m9aertner/ATtiny-PinKeepAlive/Arduino.h

/*
 * Arduino.h - Just some typedefs to make the TinySMLDecoderTest compile standalone ... 
 */
typedef unsigned char byte;
typedef unsigned char uint8_t;
typedef signed char int8_t;
typedef short unsigned int uint16_t;
typedef short signed int int16_t;
typedef signed long int32_t;
typedef unsigned long uint32_t;
typedef signed long long int64_t;
typedef unsigned long long uint64_t;
