m9aertner/ATtiny-PinKeepAlive/PinKeepAlive.h

/*
 * Variables and definitions for PinKeepAlive - Flashing the LED
 */

#ifndef __PINKEEPALIVE_H
#define __PINKEEPALIVE_H

void setupPinKeepAlive();

void pushPinEntry();

void onTickPinKeepAlive();

#endif // __PINKEEPALIVE_H
